Harsh-par/smart-monoculars/include/ov5642_configuration.h

#ifndef OV5642_CONFIGURATION_H
#define OV5642_CONFIGURATION_H

static const uint16_t ov5642_configuration[][2] = {
	{0x3103 ,0x93}, {0x3008 ,0x82}, {0x3017 ,0x7f}, {0x3018 ,0xfc},
	{0x3810 ,0xc2}, {0x3615 ,0xf0}, {0x3000 ,0x00}, {0x3001 ,0x00},
	{0x3002 ,0x5c}, {0x3003 ,0x00}, {0x3004 ,0xff}, {0x3005 ,0xff},
	{0x3006 ,0x43}, {0x3007 ,0x37}, {0x3011 ,0x20}, {0x3010 ,0x10}, 
	{0x460c ,0x22}, {0x3815 ,0x04}, {0x370c ,0xa0}, {0x3602 ,0xfc},
	{0x3612 ,0xff}, {0x3634 ,0xc0}, {0x3613 ,0x00}, {0x3605 ,0x7c},
	{0x3621 ,0x09}, {0x3622 ,0x60}, {0x3604 ,0x40}, {0x3603 ,0xa7},
	{0x3603 ,0x27}, {0x4000 ,0x21}, {0x401d ,0x22}, {0x3600 ,0x54},
	{0x3605 ,0x04}, {0x3606 ,0x3f}, {0x3c01 ,0x80}, {0x5000 ,0x4f},
	{0x5020 ,0x04}, {0x5181 ,0x79}, {0x5182 ,0x00}, {0x5185 ,0x22},
	{0x5197 ,0x01}, {0x5001 ,0xff}, {0x5500 ,0x0a}, {0x5504 ,0x00},
	{0x5505 ,0x7f}, {0x5080 ,0x08}, {0x300e ,0x18}, {0x4610 ,0x00},
	{0x471d ,0x05}, {0x4708 ,0x06}, {0x3808 ,0x02}, {0x3809 ,0x80},
	{0x380a ,0x01}, {0x380b ,0xe0}, {0x380e ,0x07}, {0x380f ,0xd0},
	{0x501f ,0x00}, {0x5000 ,0x4f}, {0x4300 ,0x32}, {0x3503 ,0x07},
	{0x3501 ,0x73}, {0x3502 ,0x80}, {0x350b ,0x00}, {0x3503 ,0x07},
	{0x3824 ,0x11}, {0x3501 ,0x1e}, {0x3502 ,0x80}, {0x350b ,0x7f},
	{0x380c ,0x0c}, {0x380d ,0x80}, {0x380e ,0x03}, {0x380f ,0xe8}, 
	{0x3a0d ,0x04}, {0x3a0e ,0x03}, {0x3818 ,0xc1}, {0x3705 ,0xdb},
	{0x370a ,0x81}, {0x3801 ,0x80}, {0x3621 ,0x87}, {0x3801 ,0x50},
	{0x3803 ,0x08}, {0x3827 ,0x08}, {0x3810 ,0x40}, {0x3804 ,0x05},
	{0x3805 ,0x00}, {0x5682 ,0x05}, {0x5683 ,0x00}, {0x3806 ,0x03},
	{0x3807 ,0xc0}, {0x5686 ,0x03}, {0x5687 ,0xbc}, {0x3a00 ,0x78},
	{0x3a1a ,0x05}, {0x3a13 ,0x30}, {0x3a18 ,0x00}, {0x3a19 ,0x7c},
	{0x3a08 ,0x12}, {0x3a09 ,0xc0}, {0x3a0a ,0x0f}, {0x3a0b ,0xa0},
	{0x350c ,0x07}, {0x350d ,0xd0}, {0x3500 ,0x00}, {0x3501 ,0x00},
	{0x3502 ,0x00}, {0x350a ,0x00}, {0x350b ,0x00}, {0x3503 ,0x00},
	{0x528a ,0x02}, {0x528b ,0x04}, {0x528c ,0x08}, {0x528d ,0x08},
	{0x528e ,0x08}, {0x528f ,0x10}, {0x5290 ,0x10}, {0x5292 ,0x00},
	{0x5293 ,0x02}, {0x5294 ,0x00}, {0x5295 ,0x02}, {0x5296 ,0x00},
	{0x5297 ,0x02}, {0x5298 ,0x00}, {0x5299 ,0x02}, {0x529a ,0x00},
	{0x529b ,0x02}, {0x529c ,0x00}, {0x529d ,0x02}, {0x529e ,0x00},
	{0x529f ,0x02}, {0x3030 ,0x0b}, {0x3a02 ,0x00}, {0x3a03 ,0x7d},
	{0x3a04 ,0x00}, {0x3a14 ,0x00}, {0x3a15 ,0x7d}, {0x3a16 ,0x00},
	{0x3a00 ,0x78}, {0x3a08 ,0x09}, {0x3a09 ,0x60}, {0x3a0a ,0x07},
	{0x3a0b ,0xd0}, {0x3a0d ,0x08}, {0x3a0e ,0x06}, {0x5193 ,0x70},
	{0x589b ,0x04}, {0x589a ,0xc5}, {0x401e ,0x20}, {0x4001 ,0x42},
	{0x401c ,0x04}, {0x528a ,0x01}, {0x528b ,0x04}, {0x528c ,0x08},
	{0x528d ,0x10}, {0x528e ,0x20}, {0x528f ,0x28}, {0x5290 ,0x30},
	{0x5292 ,0x00}, {0x5293 ,0x01}, {0x5294 ,0x00}, {0x5295 ,0x04},
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
};    

#endif
